GreenShoeGarage/ThingSpeak_MKR1010_ENVshield/Documentation/Images/Enclosure_with_PCB.png

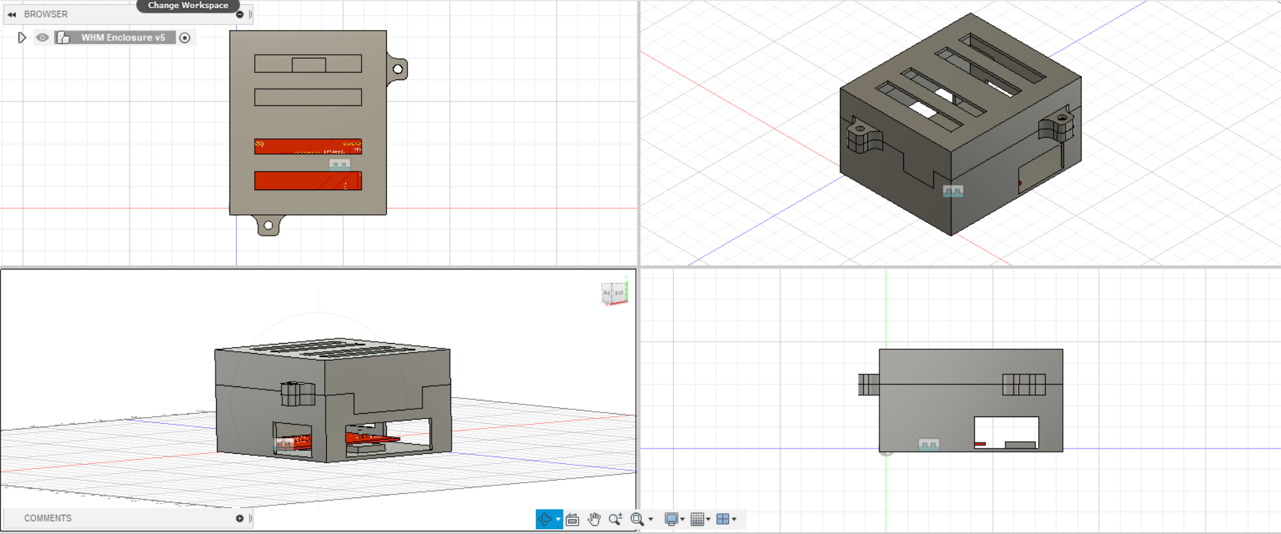
Documentation/Images/Enclosure_with_PCB.png
