GreenShoeGarage/ThingSpeak_MKR1010_ENVshield/Documentation/Images/ThingSpeak_Metrics01.png

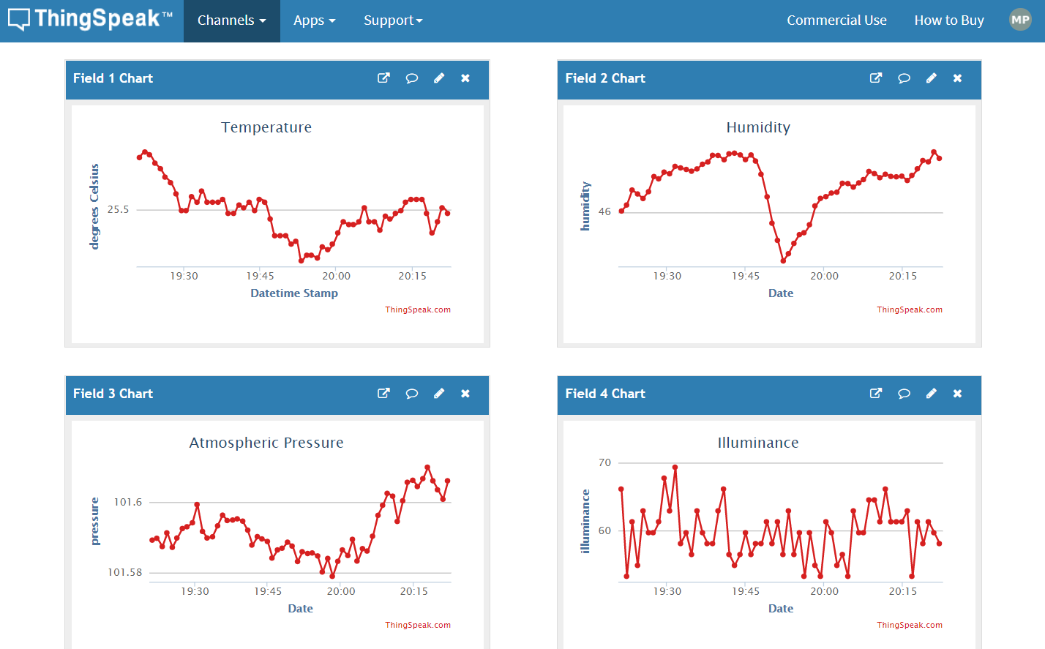
Documentation/Images/ThingSpeak_Metrics01.png
