GreenShoeGarage/ThingSpeak_MKR1010_ENVshield/Documentation/Images/WorkspaceHealthMonitor_SCH.png

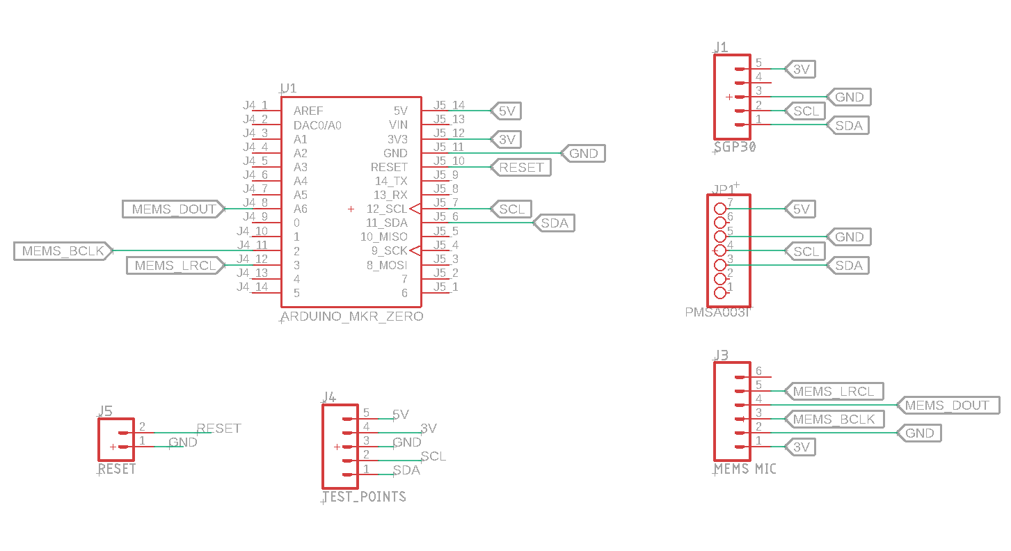
Documentation/Images/WorkspaceHealthMonitor_SCH.png
