GreenShoeGarage/ThingSpeak_MKR1010_ENVshield/Documentation/Images/WorkspaceHealthMonitor_v002_PCB.png

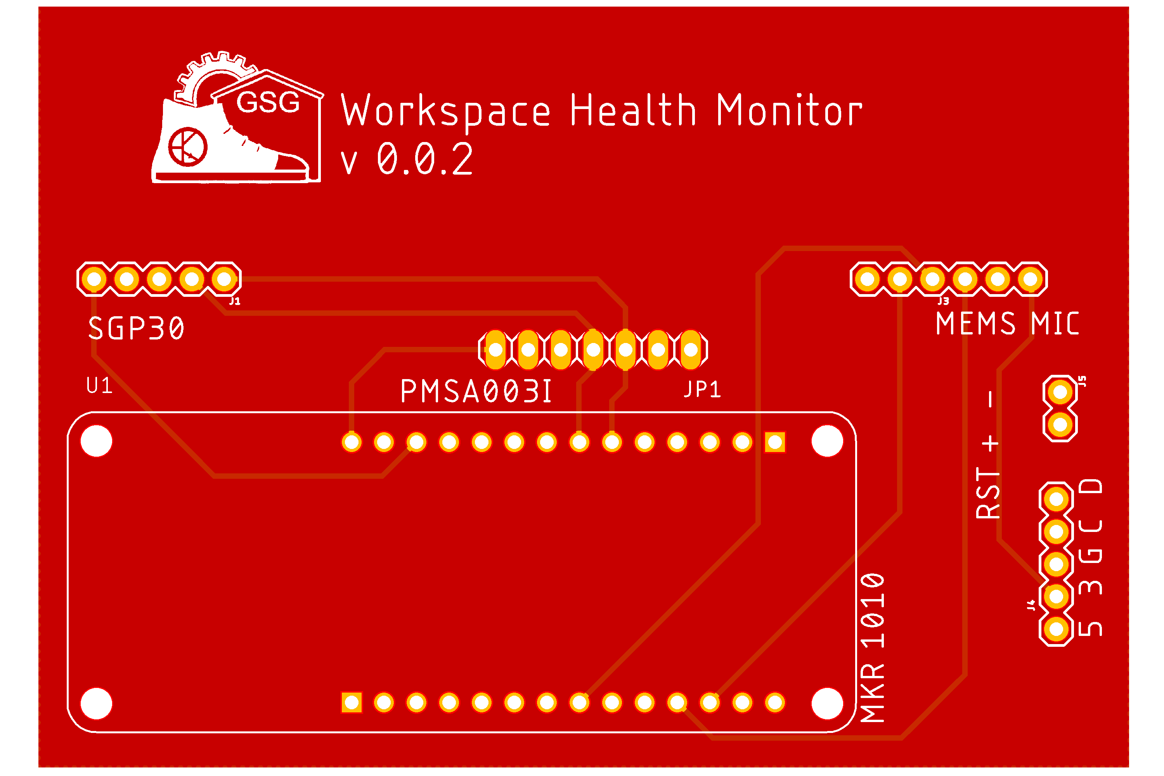
Documentation/Images/WorkspaceHealthMonitor_v002_PCB.png
